SunGema/Bras_Manipulateur_V2.0/Version2.1/Assemblage_HANDrew.SLDASM

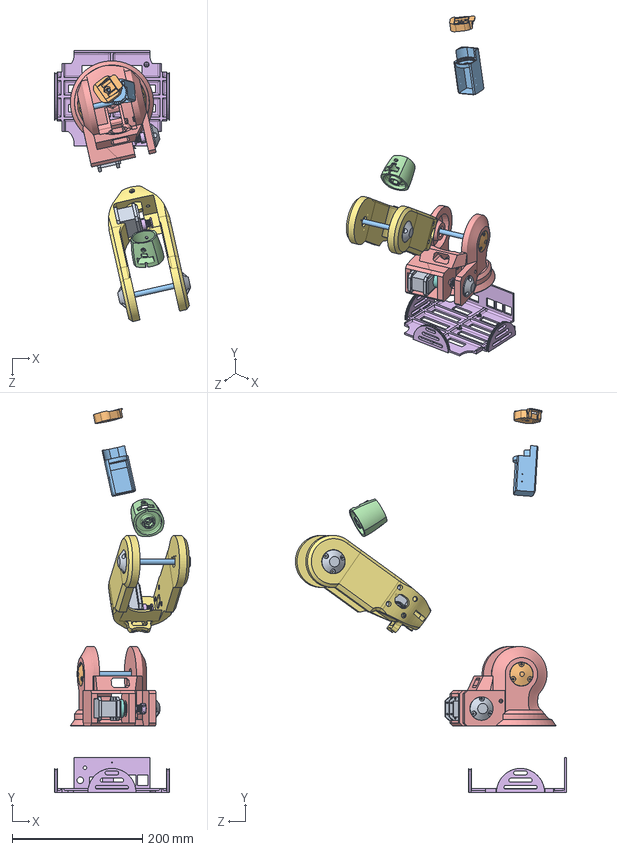
[picture p16: CAD file, 2024-02-01]
Version2.1/Assemblage_HANDrew.SLDASM
209.5 x 589.8 x 416.6 mm
support_bas
my_shoulder
my_bottom_arm
berceau_moteur
my_hand
Dynamixe_motor x 2
Support roue synchrone 2
Arm_top_V3
Roue syncrhone 2GT 20 dents x 2
bearing_e_8_01 x 7
bearing_e_8_02 x 7
Tige8x95 x 2
my_cache_shoulder x 2
my_cache_elbow x 3
