SunGema/Bras_Manipulateur_V2.0/Version 2.2 Final/Nouvelle pièce/Assemblage_Notice.SLDASM

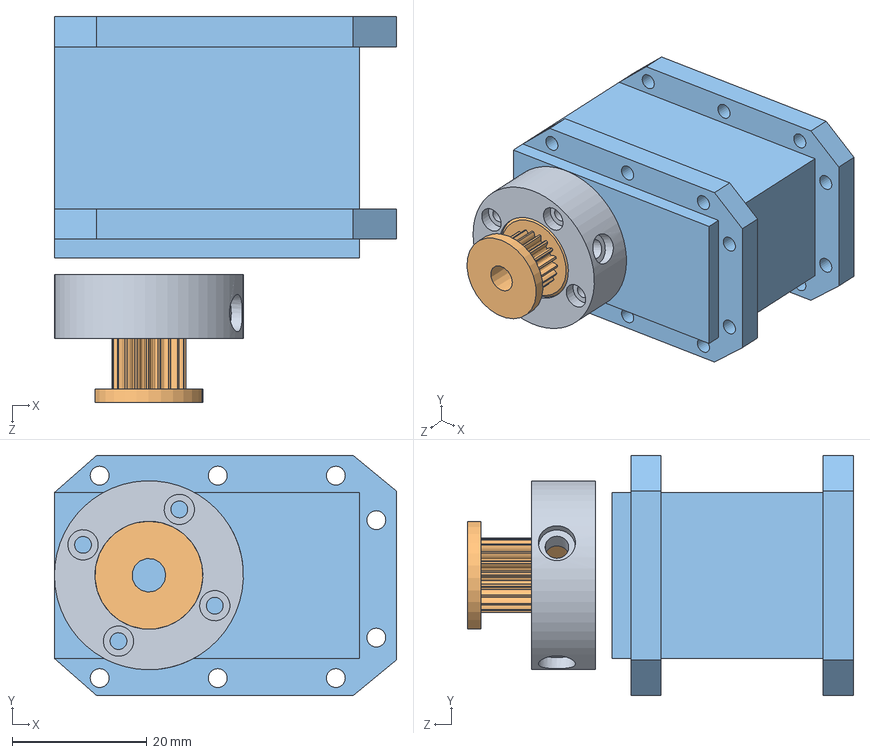
[picture p18: CAD file, 2024-02-01]
Version 2.2 Final/Nouvelle pièce/Assemblage_Notice.SLDASM
50.7 x 35.6 x 57.2 mm
Dynamixe_motor
Roue syncrhone 2GT 20 dents
Support roue synchrone 2
