SunGema/Bras_Manipulateur_V2.0/Version 2.2 Final/Nouvelle pièce/Assem2.SLDASM

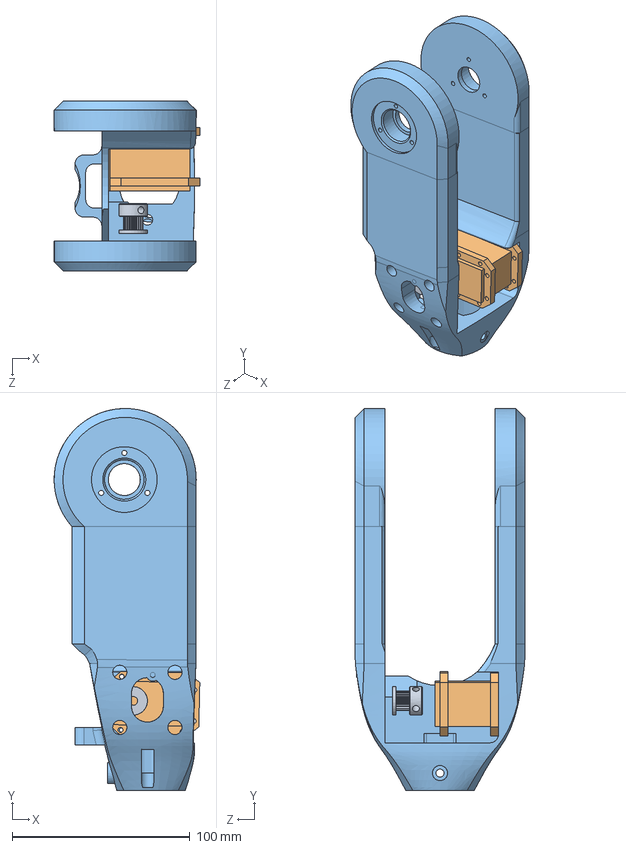
[picture p19: CAD file, 2024-02-01]
Version 2.2 Final/Nouvelle pièce/Assem2.SLDASM
82.0 x 215.0 x 95.4 mm
Arm_top_V3
Dynamixe_motor
Roue syncrhone 2GT 20 dents
