SunGema/Bras_Manipulateur_V2.0/Version 2.2 Final/Nouvelle pièce/Support roue synchrone.STL

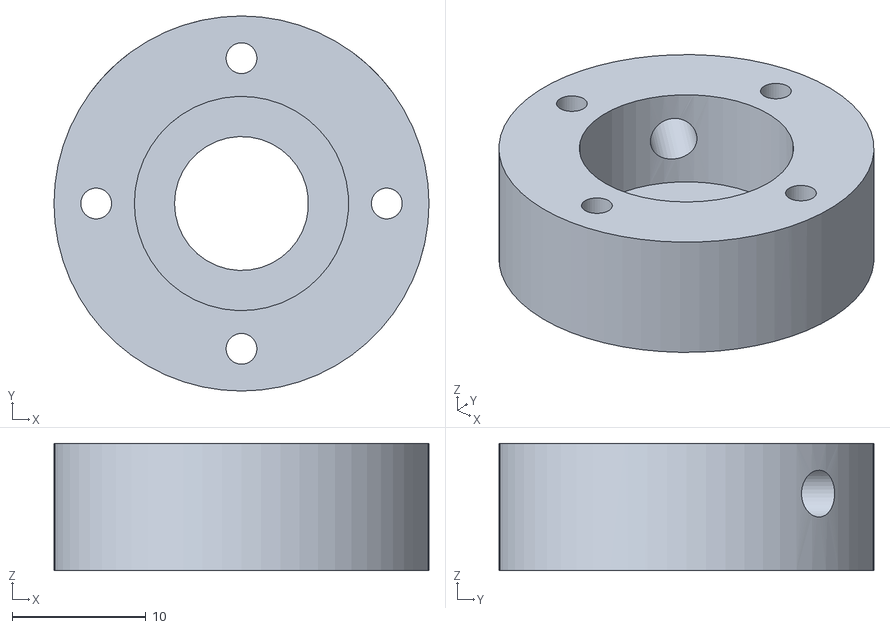
[picture p32: CAD file, 2024-02-01]
Version 2.2 Final/Nouvelle pièce/Support roue synchrone.STL
28.0 x 28.0 x 9.50
