SunGema/Bras_Manipulateur_V2.0/Version 2.2 Final/Tige/Tige8x95.SLDPRT

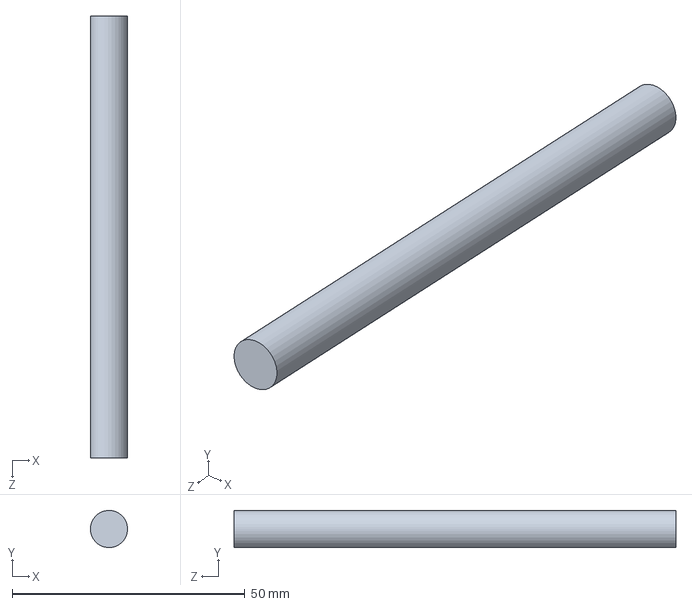
[picture p33: CAD file, 2023-12-30]
Version 2.2 Final/Tige/Tige8x95.SLDPRT
8.00 x 7.99 x 95.0 mm
