SunGema/Bras_Manipulateur_V2.0/Version2.1/143539572-7-bearing_e_8/bearing_e_8_02.SLDPRT

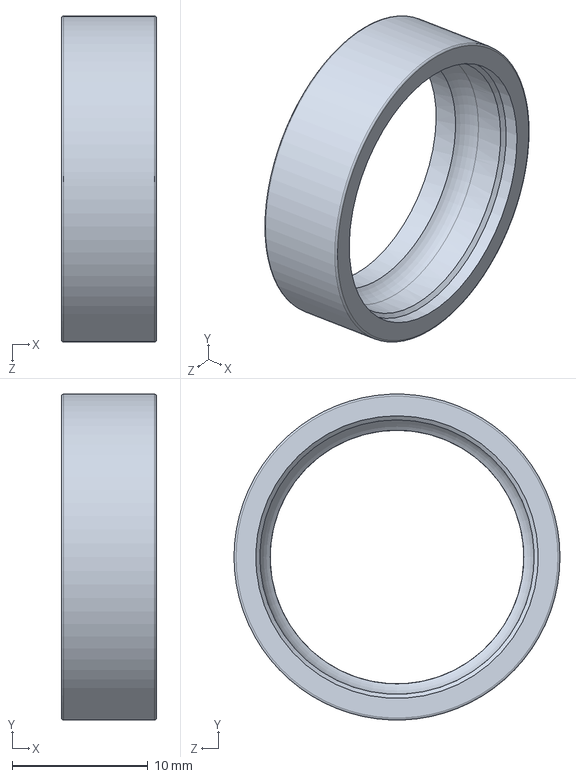
[picture p34: CAD file, 2023-12-30]
Version2.1/143539572-7-bearing_e_8/bearing_e_8_02.SLDPRT
7.00 x 24.0 x 24.0 mm
