SunGema/Bras_Manipulateur_V2.0/Version2.1/Courroie_Transmission_Base/Arm_top_V3.SLDPRT

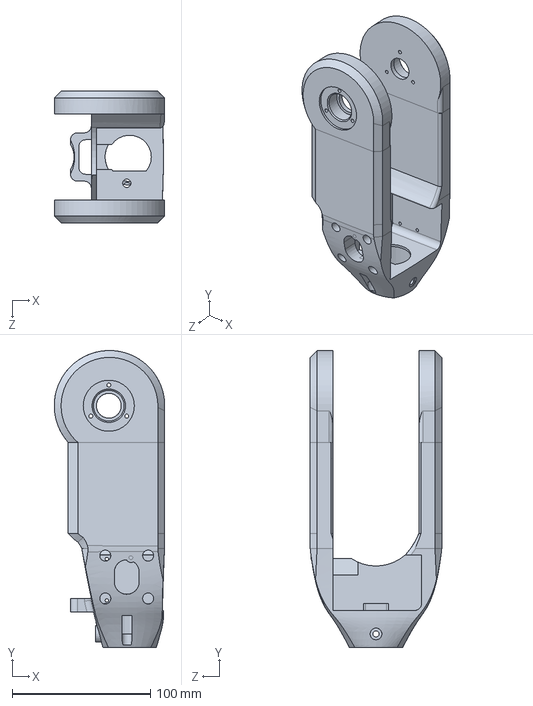
[picture p35: CAD file, 2023-11-22]
Version2.1/Courroie_Transmission_Base/Arm_top_V3.SLDPRT
80.0 x 215.0 x 95.4 mm
