SunGema/Bras_Manipulateur_V2.0/Version2.1/New_base/support_moteur_base.SLDPRT

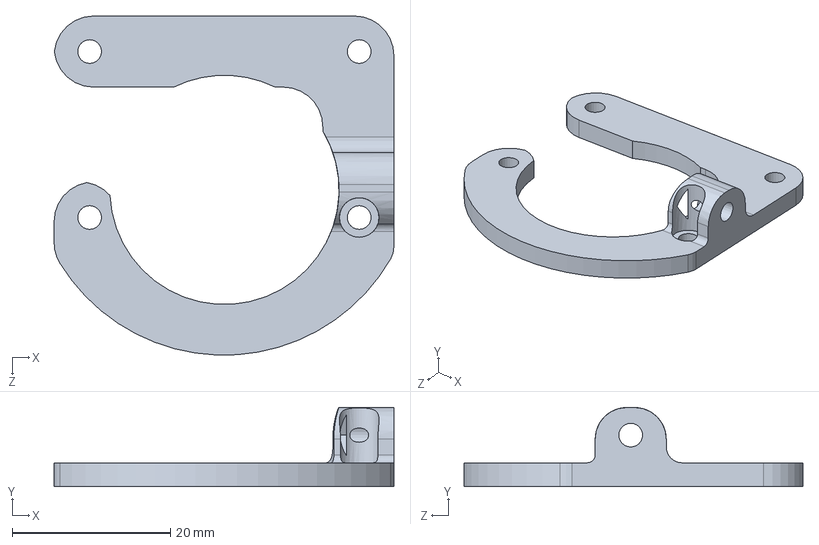
[picture p36: CAD file, 2023-12-30]
Version2.1/New_base/support_moteur_base.SLDPRT
43.0 x 10.0 x 42.9 mm
