SunGema/Bras_Manipulateur_V2.0/Version2.1/New_elbow/My_arm_top/my_arm_top_down.SLDPRT

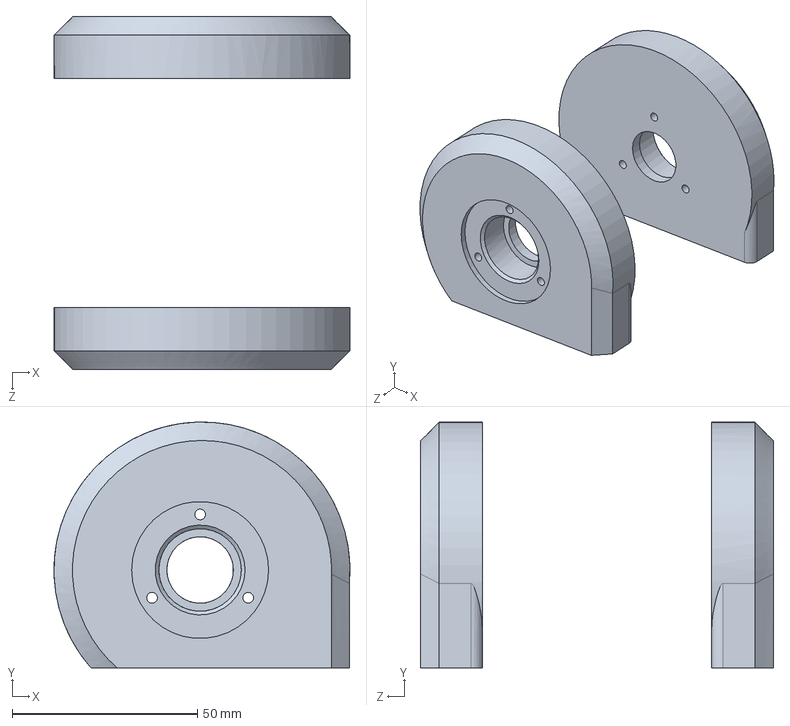
[picture p37: CAD file, 2023-12-30]
Version2.1/New_elbow/My_arm_top/my_arm_top_down.SLDPRT
80.0 x 66.5 x 95.4 mm
