SunGema/Bras_Manipulateur_V2.0/Version2.1/New_elbow/Train_epicycloidal/engrenage_satellite.SLDPRT

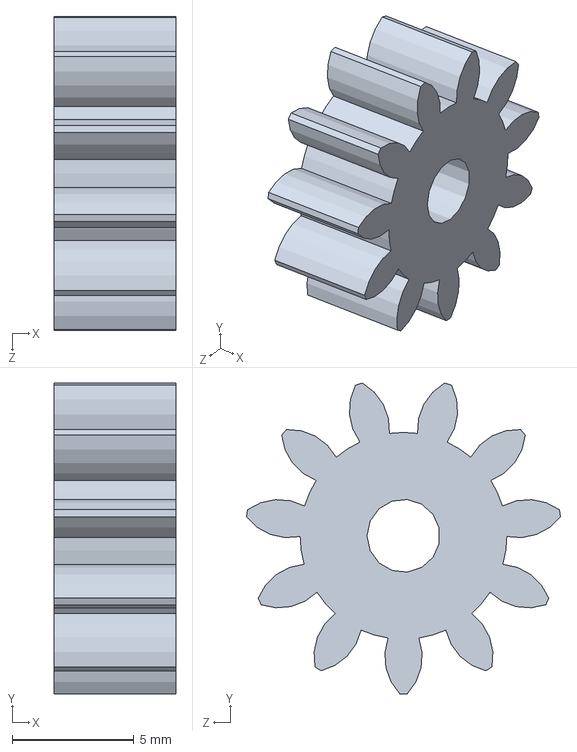
[picture p38: CAD file, 2023-12-30]
Version2.1/New_elbow/Train_epicycloidal/engrenage_satellite.SLDPRT
5.00 x 12.8 x 12.9 mm
