SunGema/Bras_Manipulateur_V2.0/Version2.1/New_shoulder/my_cache_shoulder.SLDPRT

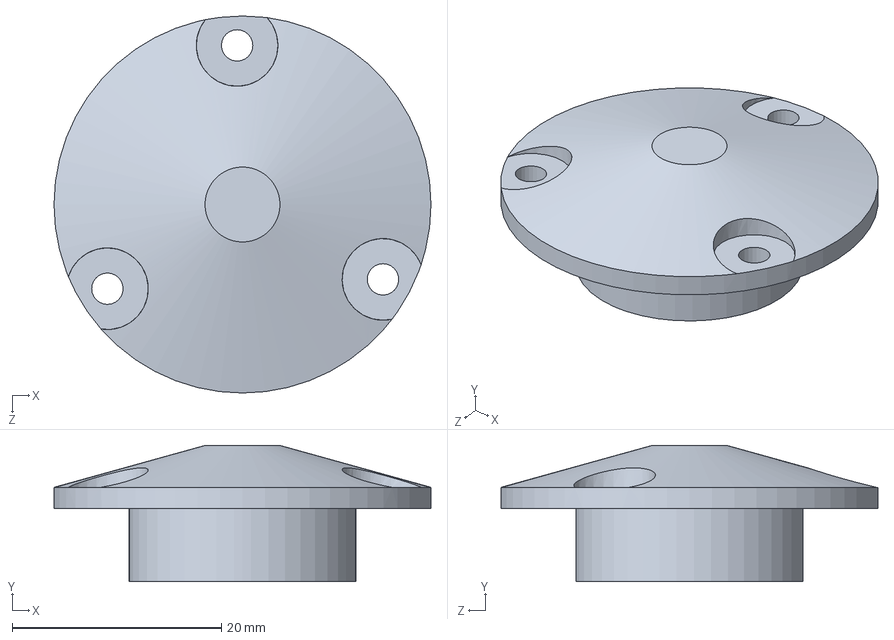
[picture p39: CAD file, 2024-02-01]
Version2.1/New_shoulder/my_cache_shoulder.SLDPRT
36.0 x 13.0 x 36.0 mm
