SunGema/Bras_Manipulateur_V2.0/Version2.1/New_wirst/STL/my_fore_arm_top.STL

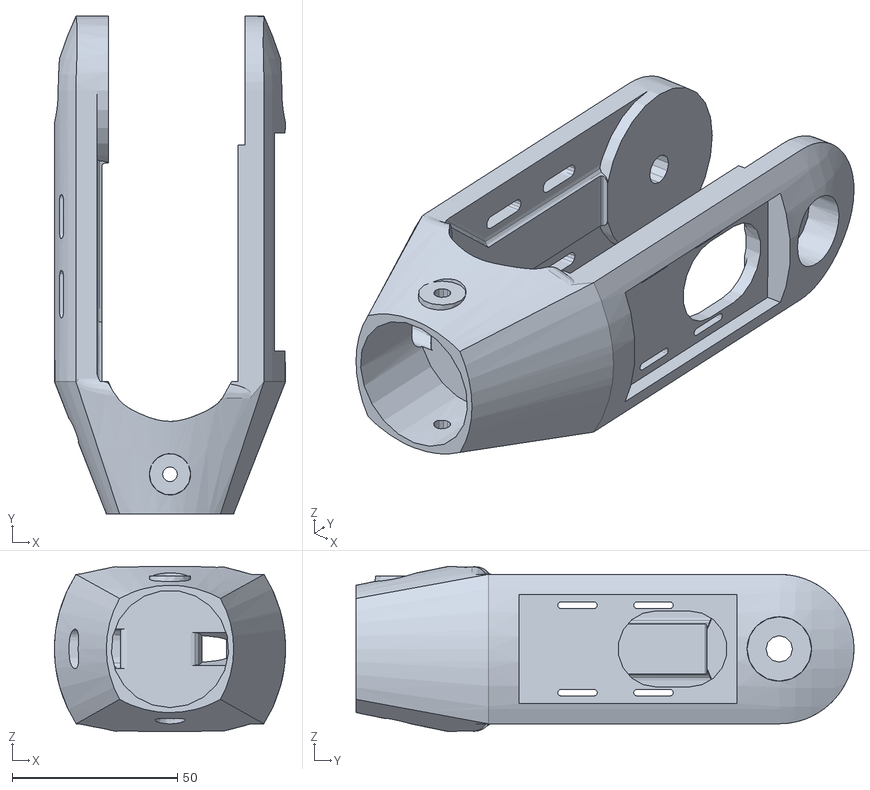
[picture p40: CAD file, 2023-12-30]
Version2.1/New_wirst/STL/my_fore_arm_top.STL
69.9 x 150.6 x 50.0
