SunGema/Bras_Manipulateur_V2.0/Version 2.2 Final/Dynamixe_motor.SLDPRT

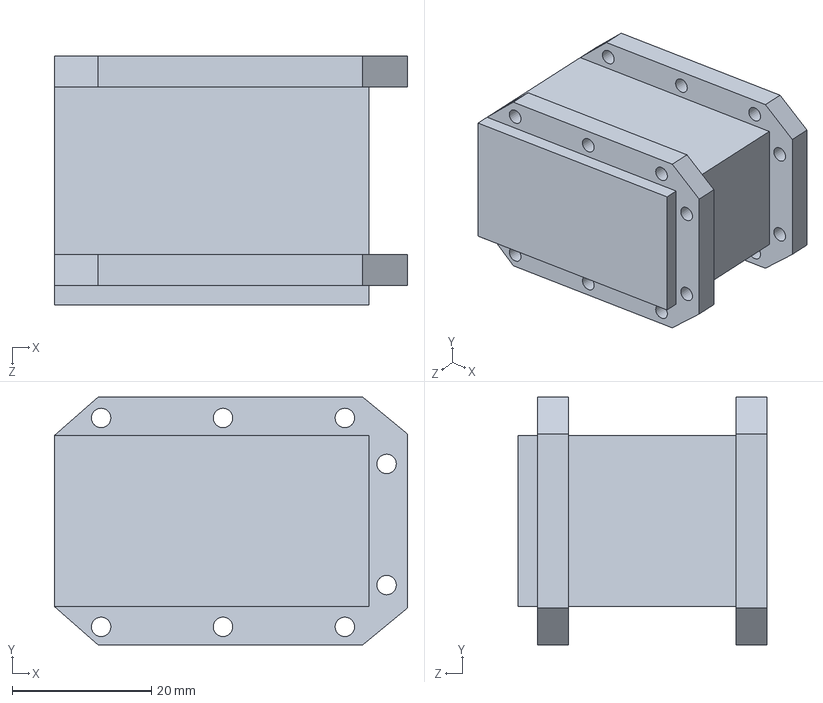
[picture p41: CAD file, 2023-12-30]
Version 2.2 Final/Dynamixe_motor.SLDPRT
50.7 x 35.6 x 35.8 mm
