SunGema/Bras_Manipulateur_V2.0/Version 2.2 Final/New_base/fixation_g.SLDPRT

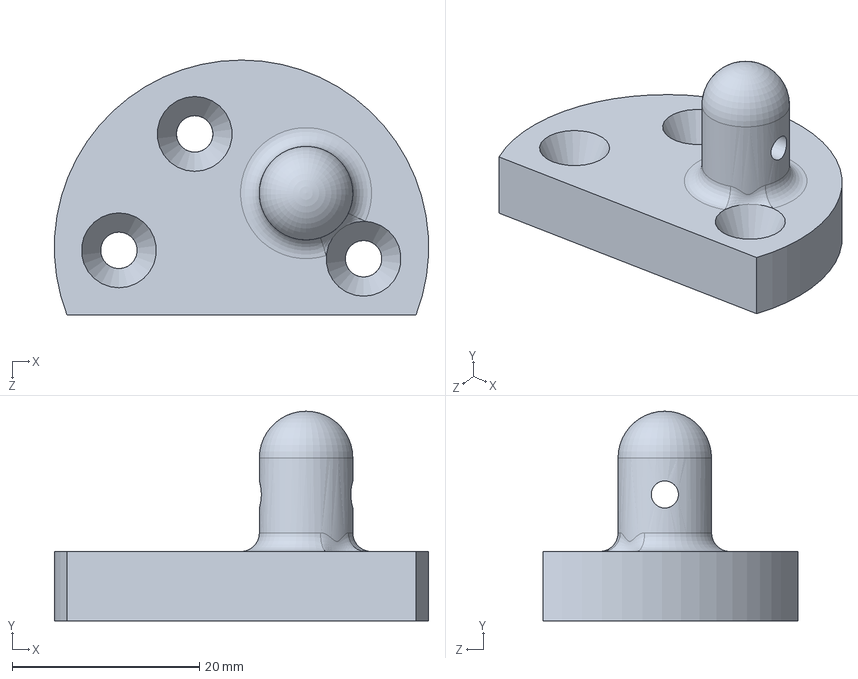
[picture p42: CAD file, 2023-12-30]
Version 2.2 Final/New_base/fixation_g.SLDPRT
40.0 x 22.4 x 27.2 mm
