SunGema/Bras_Manipulateur_V2.0/Version 2.2 Final/New_elbow/My_arm_top/my_arm_top_final.SLDPRT

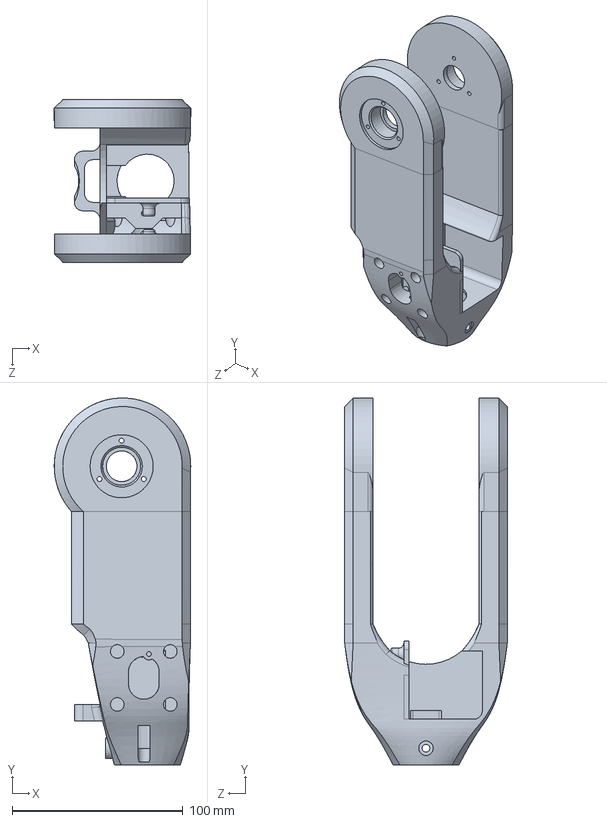
[picture p43: CAD file, 2023-12-30]
Version 2.2 Final/New_elbow/My_arm_top/my_arm_top_final.SLDPRT
80.0 x 215.0 x 95.4 mm
