SunGema/Bras_Manipulateur_V2.0/Version 2.2 Final/New_elbow/my_bottom_arm.SLDPRT

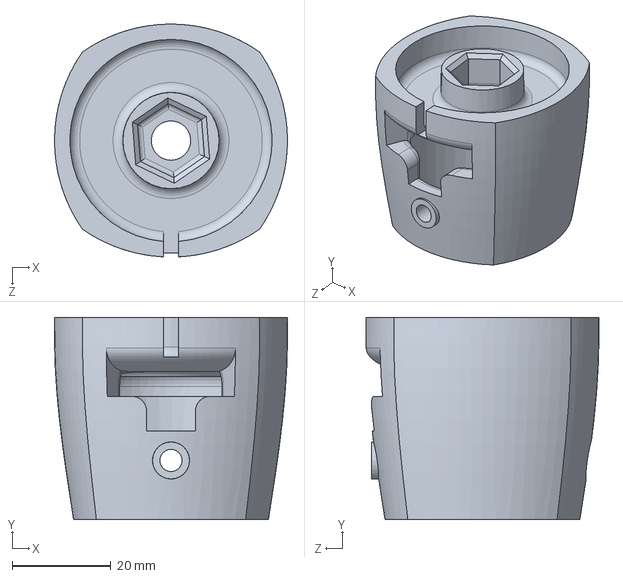
[picture p44: CAD file, 2023-12-30]
Version 2.2 Final/New_elbow/my_bottom_arm.SLDPRT
47.2 x 41.0 x 47.2 mm
