SunGema/Bras_Manipulateur_V2.0/Version 2.2 Final/New_elbow/Train_epicycloidal/bloc.SLDPRT

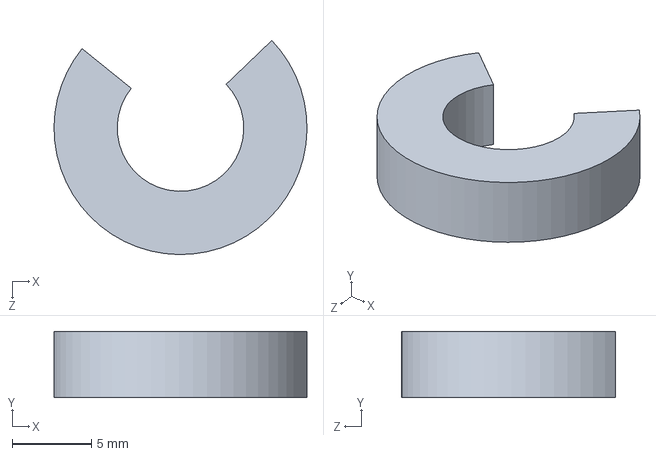
[picture p45: CAD file, 2023-12-30]
Version 2.2 Final/New_elbow/Train_epicycloidal/bloc.SLDPRT
16.0 x 4.20 x 13.5 mm
