SunGema/Bras_Manipulateur_V2.0/Version 2.2 Final/New_wirst/engrenage_moteur_wirst.SLDPRT

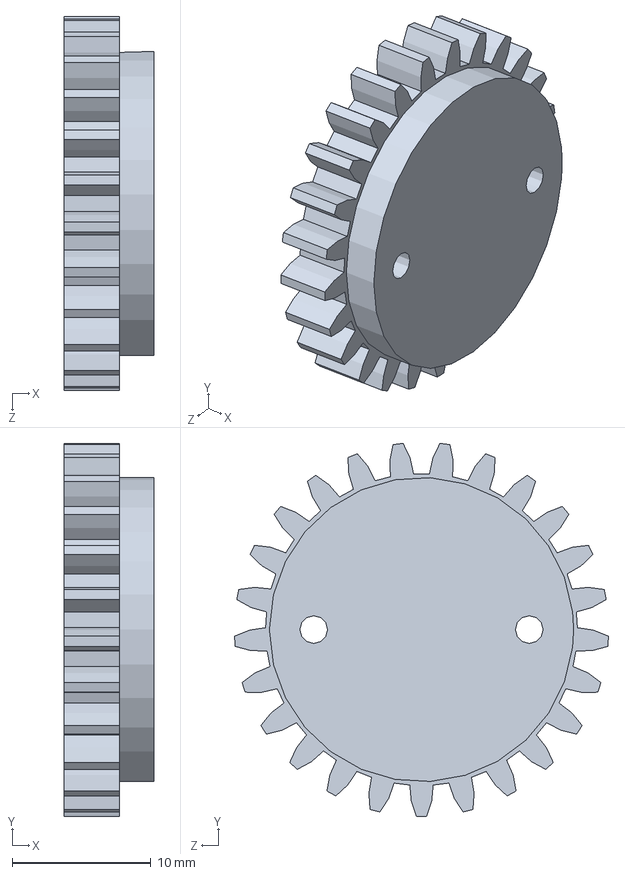
[picture p46: CAD file, 2023-12-30]
Version 2.2 Final/New_wirst/engrenage_moteur_wirst.SLDPRT
6.50 x 26.9 x 27.0 mm
