SunGema/Bras_Manipulateur_V2.0/Version 2.2 Final/New_wirst/Train_epicycloidal/satellite_wirst.SLDPRT

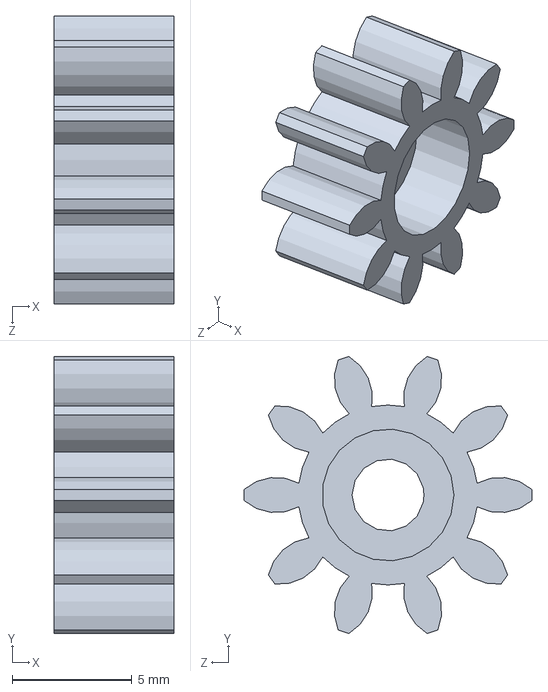
[picture p47: CAD file, 2023-12-30]
Version 2.2 Final/New_wirst/Train_epicycloidal/satellite_wirst.SLDPRT
5.00 x 11.5 x 12.0 mm
