SunGema/Bras_Manipulateur_V2.0/Version 2.2 Final/Tige/Tige8x25.SLDPRT

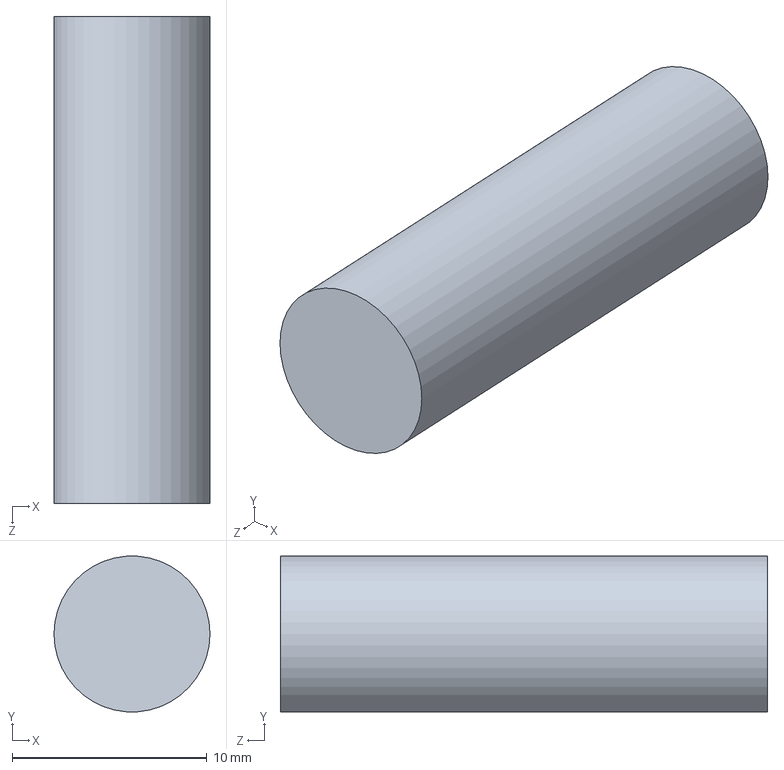
[picture p48: CAD file, 2023-12-30]
Version 2.2 Final/Tige/Tige8x25.SLDPRT
8.00 x 7.98 x 25.0 mm
