SunGema/Bras_Manipulateur_V2.0/Version2.1/New_elbow/couvercle.SLDPRT

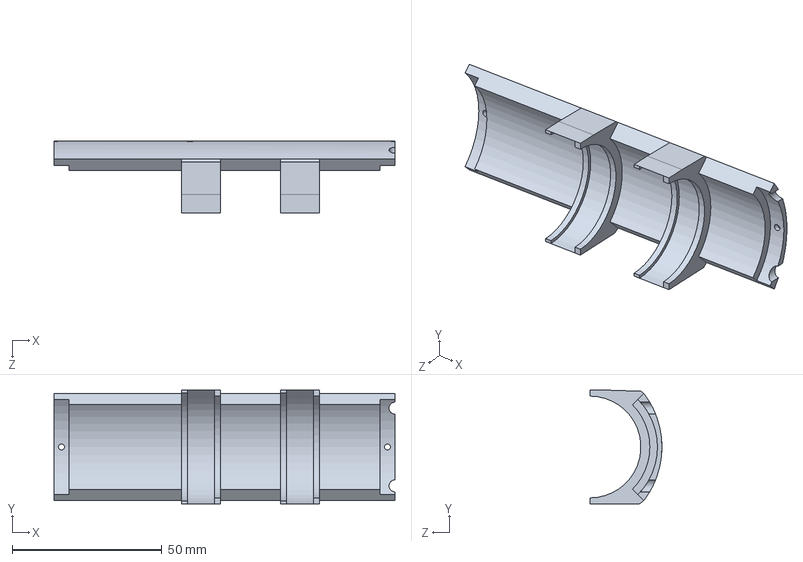
[picture p49: CAD file, 2023-12-30]
Version2.1/New_elbow/couvercle.SLDPRT
114.0 x 38.0 x 24.0 mm
