SunGema/Bras_Manipulateur_V2.0/Version2.1/New_shoulder/my_shoulder.SLDPRT

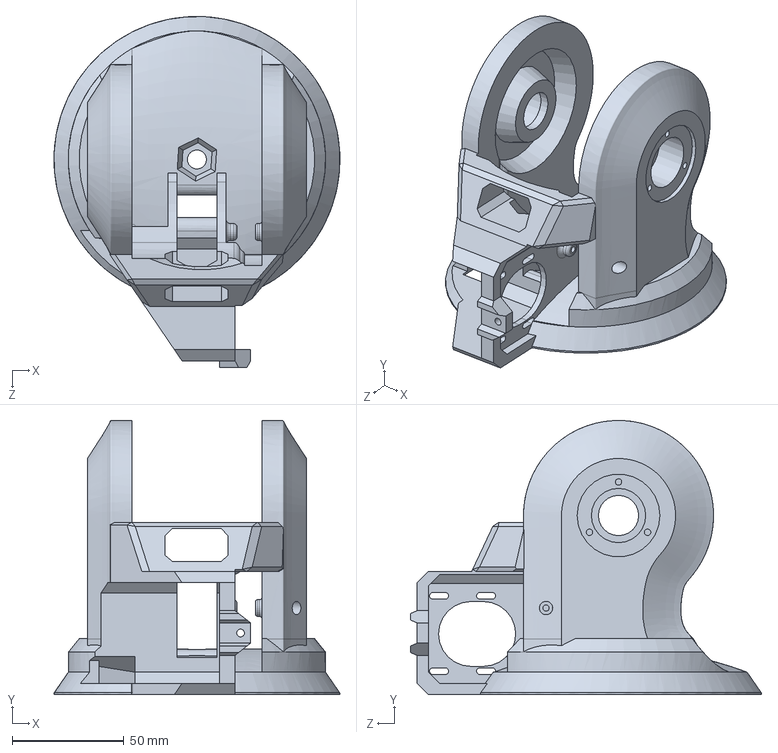
[picture p50: CAD file, 2024-02-01]
Version2.1/New_shoulder/my_shoulder.SLDPRT
127.8 x 122.5 x 156.9 mm
