SunGema/Bras_Manipulateur_V2.0/Version 2.2 Final/New_base/my_base_bearing_support.SLDPRT

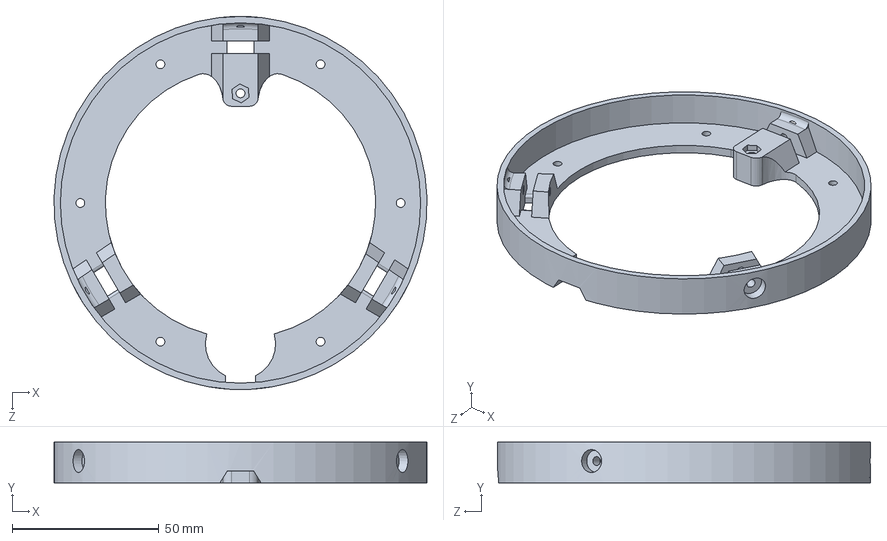
[picture p51: CAD file, 2023-12-30]
Version 2.2 Final/New_base/my_base_bearing_support.SLDPRT
126.9 x 13.8 x 127.0 mm
