SunGema/Bras_Manipulateur_V2.0/Version 2.2 Final/New_elbow/engrenage_moteur_elbow_part2.SLDPRT

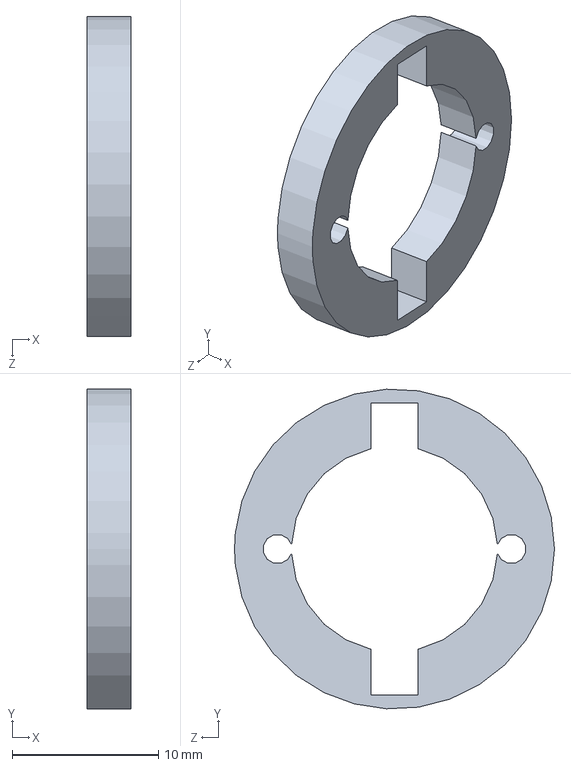
[picture p52: CAD file, 2023-12-30]
Version 2.2 Final/New_elbow/engrenage_moteur_elbow_part2.SLDPRT
3.00 x 21.9 x 21.9 mm
