SunGema/Bras_Manipulateur_V2.0/Version 2.2 Final/New_elbow/My_arm_top/my_arm_top_up.SLDPRT

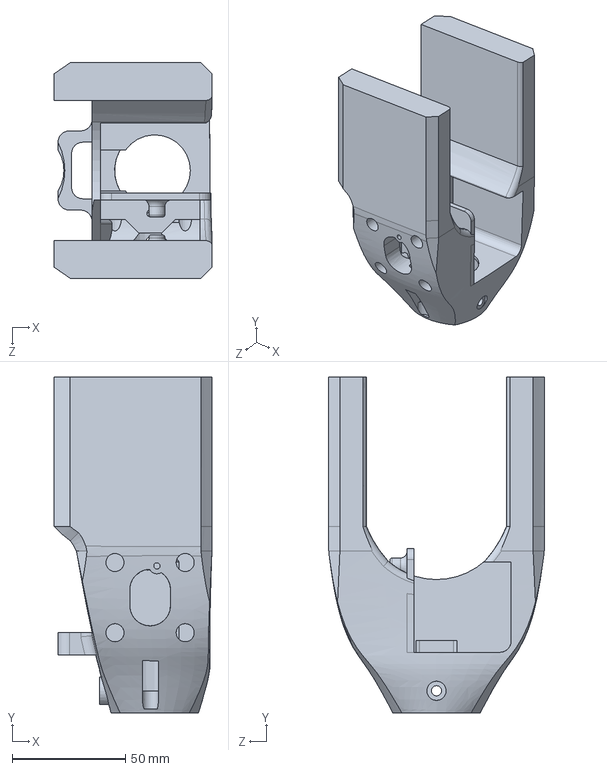
[picture p53: CAD file, 2023-12-30]
Version 2.2 Final/New_elbow/My_arm_top/my_arm_top_up.SLDPRT
69.8 x 148.5 x 95.4 mm
