SunGema/Bras_Manipulateur_V2.0/Version 2.2 Final/New_elbow/Train_epicycloidal/planetaire.SLDPRT

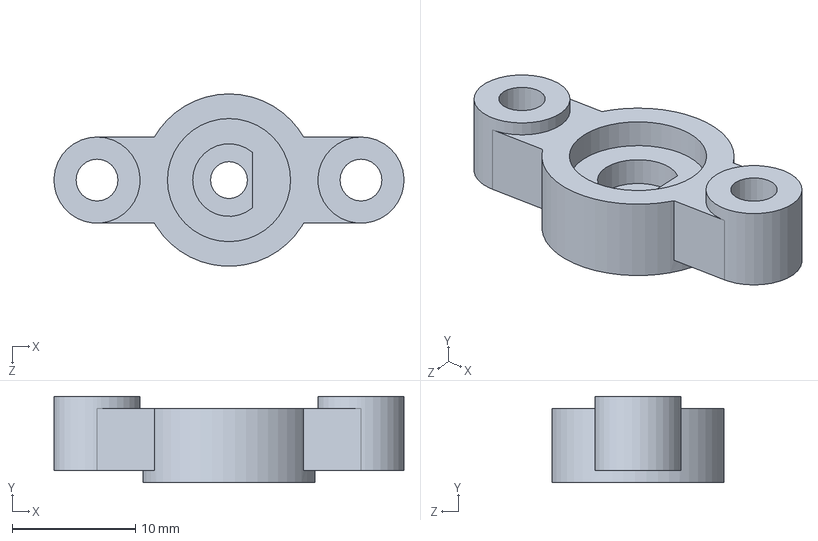
[picture p54: CAD file, 2023-12-30]
Version 2.2 Final/New_elbow/Train_epicycloidal/planetaire.SLDPRT
28.4 x 7.00 x 14.0 mm
