SunGema/Bras_Manipulateur_V2.0/Version 2.2 Final/New_shoulder/my_roundtube.SLDPRT

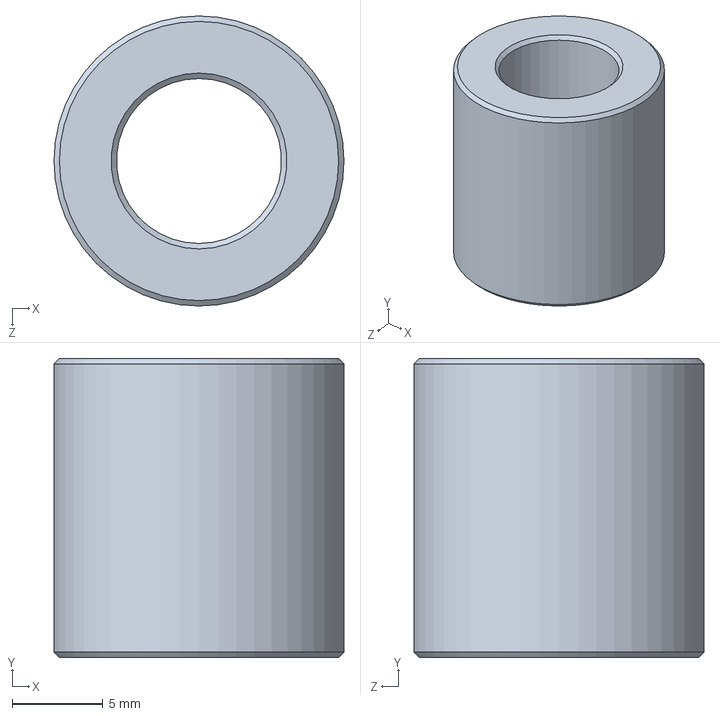
[picture p55: CAD file, 2023-12-30]
Version 2.2 Final/New_shoulder/my_roundtube.SLDPRT
16.0 x 16.5 x 16.0 mm
