SunGema/Bras_Manipulateur_V2.0/Version 2.2 Final/Tige/Tige8x45.SLDPRT

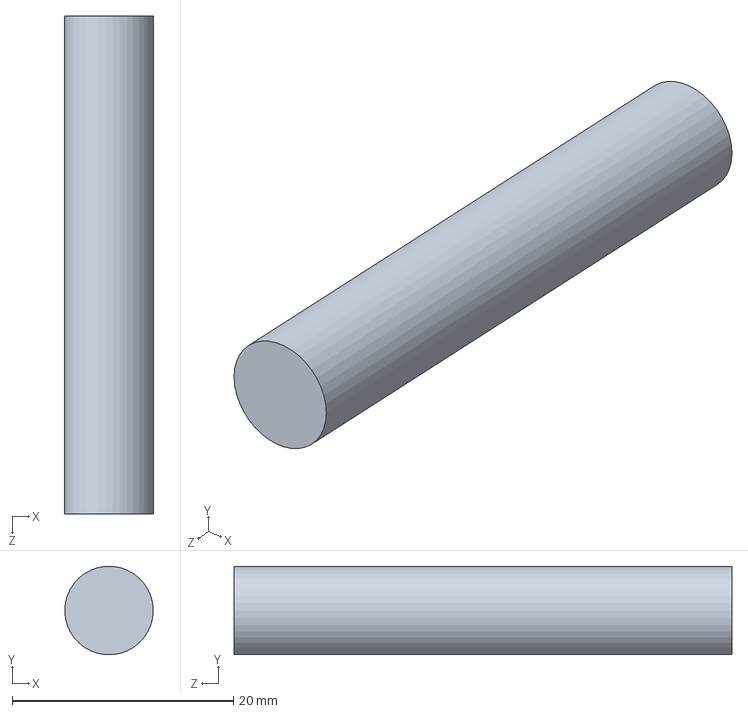
[picture p56: CAD file, 2023-12-30]
Version 2.2 Final/Tige/Tige8x45.SLDPRT
8.00 x 7.97 x 45.0 mm
