SunGema/Bras_Manipulateur_V2.0/Version 2.2 Final/tube_bottom.SLDPRT

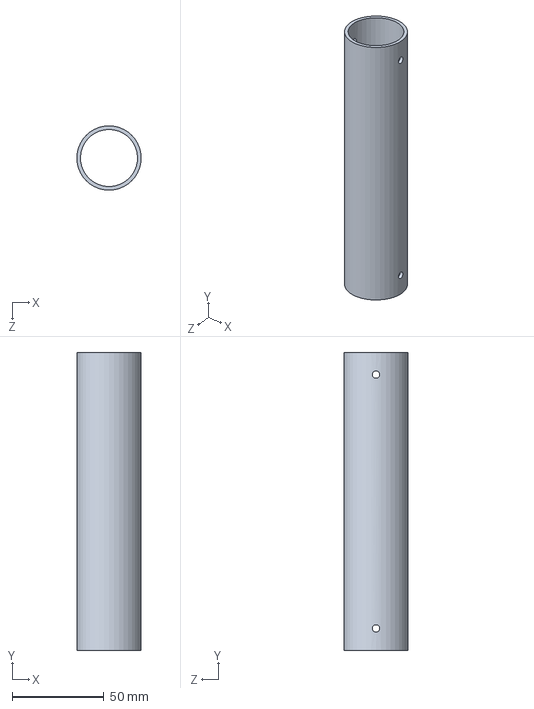
[picture p57: CAD file, 2023-12-30]
Version 2.2 Final/tube_bottom.SLDPRT
35.0 x 162.0 x 35.0 mm
