SunGema/Bras_Manipulateur_V2.0/Version2.1/143539572-7-bearing_e_8/bearing_e_8_03.SLDPRT

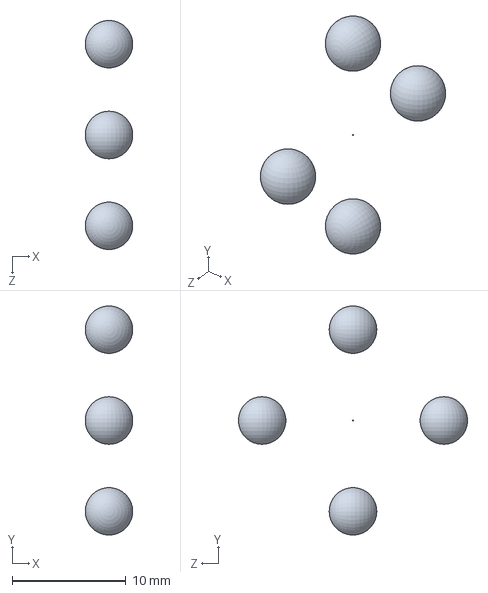
[picture p58: CAD file, 2023-12-30]
Version2.1/143539572-7-bearing_e_8/bearing_e_8_03.SLDPRT
4.18 x 20.2 x 20.2 mm
