SunGema/Bras_Manipulateur_V2.0/Version2.1/New_elbow/support_moteur.SLDPRT

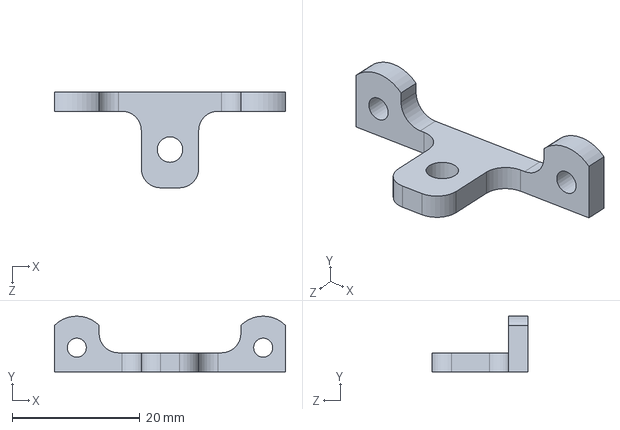
[picture p59: CAD file, 2023-12-30]
Version2.1/New_elbow/support_moteur.SLDPRT
36.2 x 8.75 x 15.0 mm
