SunGema/Bras_Manipulateur_V2.0/Version2.1/New_wirst/berceau_axe.SLDPRT

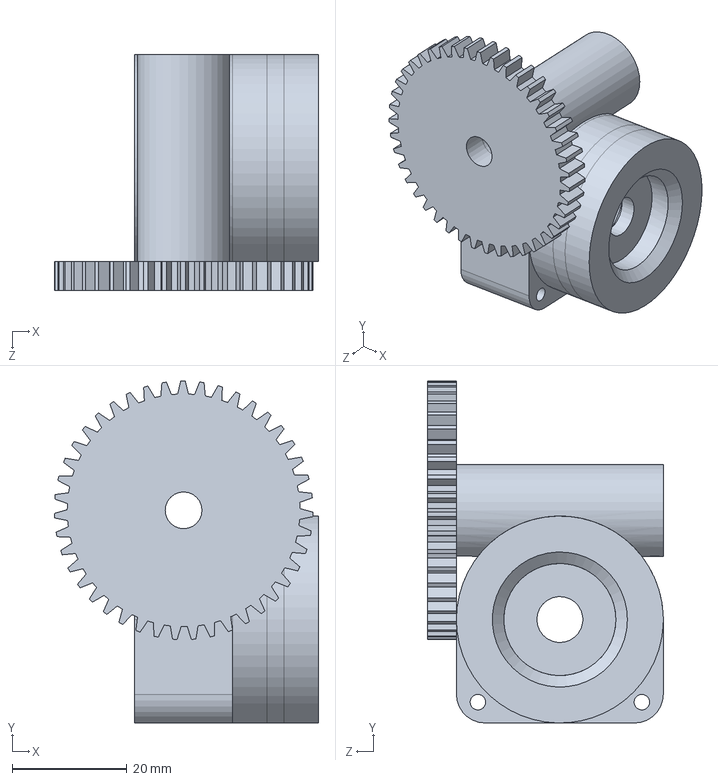
[picture p60: CAD file, 2023-12-30]
Version2.1/New_wirst/berceau_axe.SLDPRT
46.0 x 59.5 x 41.0 mm
