SunGema/Bras_Manipulateur_V2.0/Version2.1/New_wirst/Train_epicycloidal/accroche_vis_berceau.SLDPRT

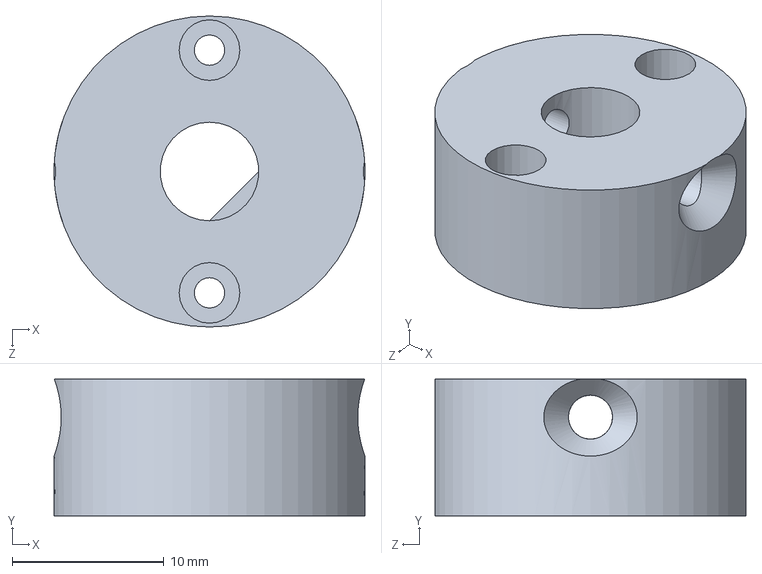
[picture p61: CAD file, 2023-12-30]
Version2.1/New_wirst/Train_epicycloidal/accroche_vis_berceau.SLDPRT
20.5 x 9.00 x 20.5 mm
