SunGema/Bras_Manipulateur_V2.0/Version2.1/tube_top.SLDPRT

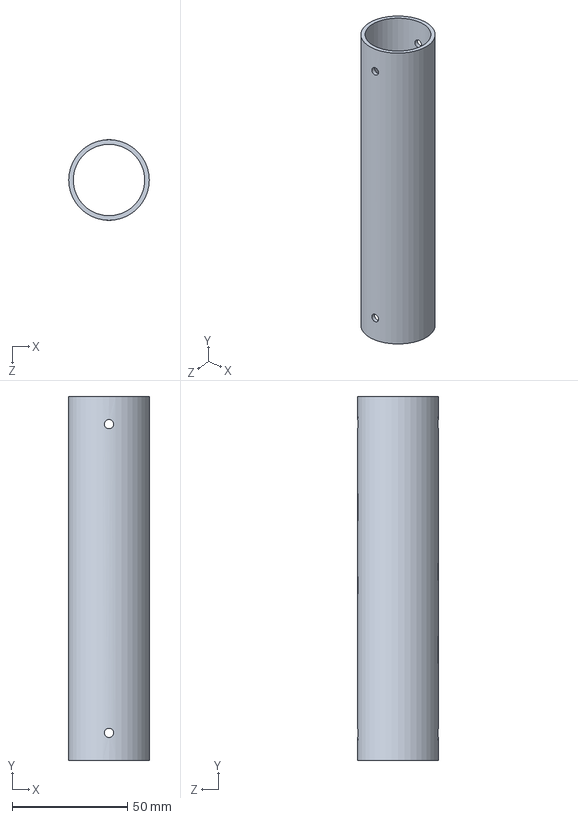
[picture p62: CAD file, 2023-12-30]
Version2.1/tube_top.SLDPRT
35.0 x 158.0 x 35.0 mm
