SunGema/Bras_Manipulateur_V2.0/Version 2.2 Final/New_elbow/Train_epicycloidal/planetaire_fin.SLDPRT

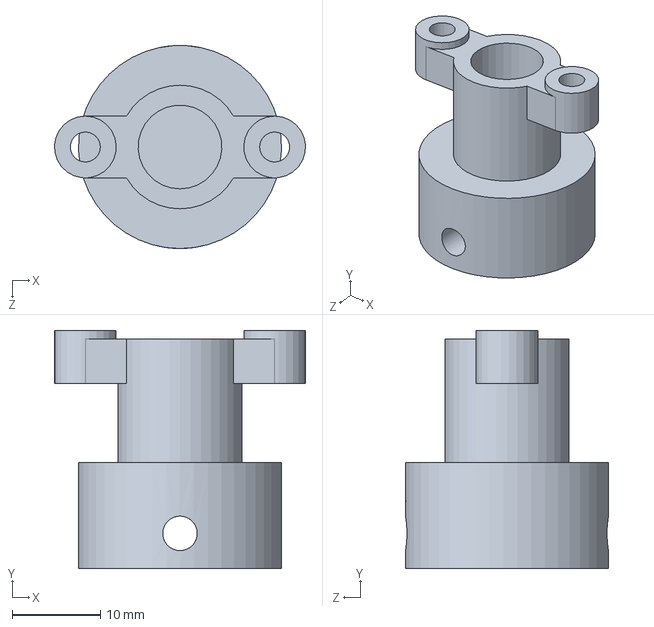
[picture p63: CAD file, 2023-12-30]
Version 2.2 Final/New_elbow/Train_epicycloidal/planetaire_fin.SLDPRT
28.4 x 27.0 x 23.0 mm
