SunGema/Bras_Manipulateur_V2.0/Version 2.2 Final/New_shoulder/engrenage_moteur_shoulder_part2.SLDPRT

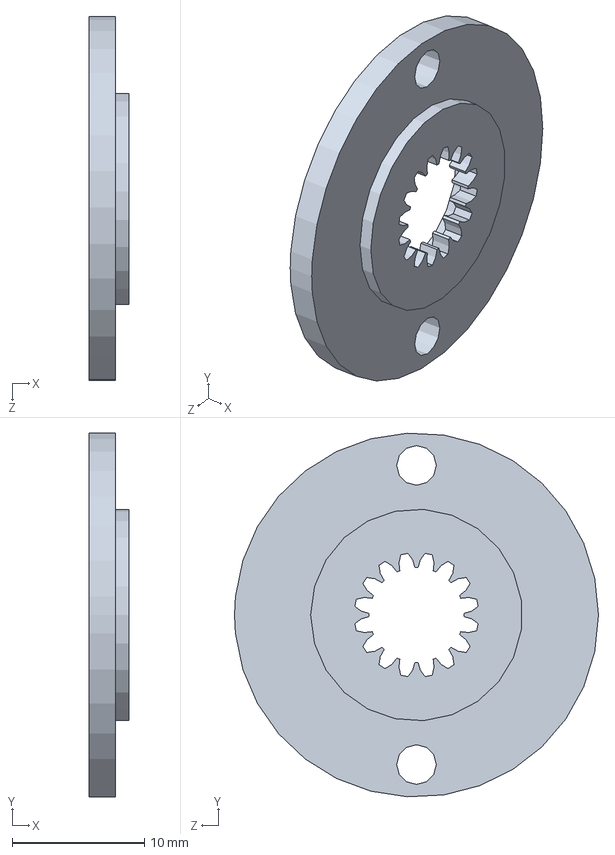
[picture p64: CAD file, 2023-12-30]
Version 2.2 Final/New_shoulder/engrenage_moteur_shoulder_part2.SLDPRT
3.00 x 27.5 x 27.5 mm
