SunGema/Bras_Manipulateur_V2.0/Version 2.2 Final/Nouvelle pièce/Support roue synchrone 2.SLDPRT

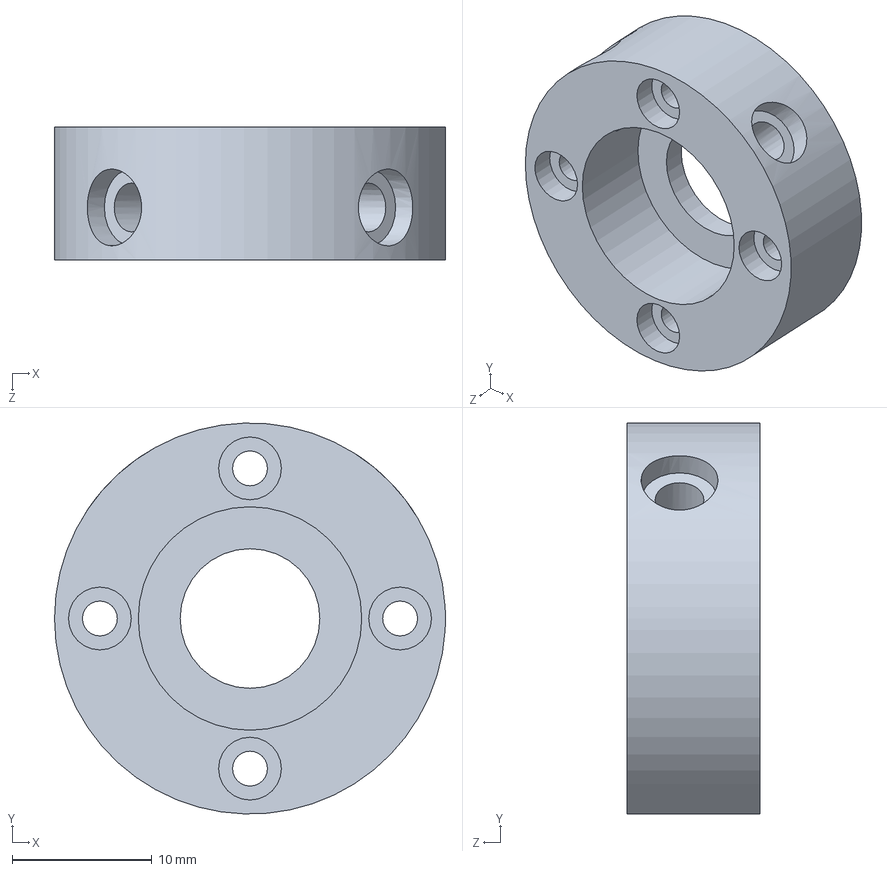
[picture p65: CAD file, 2024-02-01]
Version 2.2 Final/Nouvelle pièce/Support roue synchrone 2.SLDPRT
28.0 x 28.0 x 9.50 mm
