SunGema/Bras_Manipulateur_V2.0/Version2.1/New_elbow/accroche_vis.SLDPRT

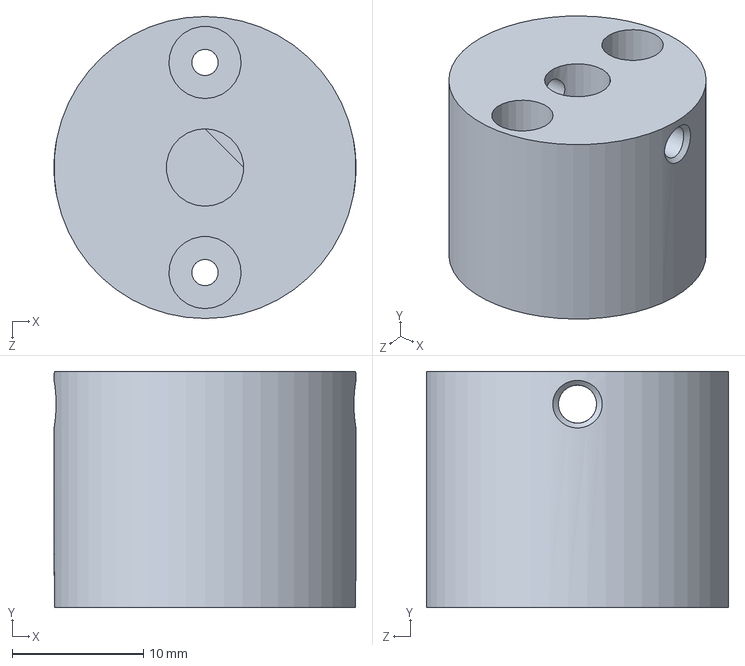
[picture p66: CAD file, 2023-12-30]
Version2.1/New_elbow/accroche_vis.SLDPRT
23.0 x 18.0 x 23.0 mm
