SunGema/Bras_Manipulateur_V2.0/Version2.1/New_shoulder/engrenage_moteur_shoulder.SLDPRT

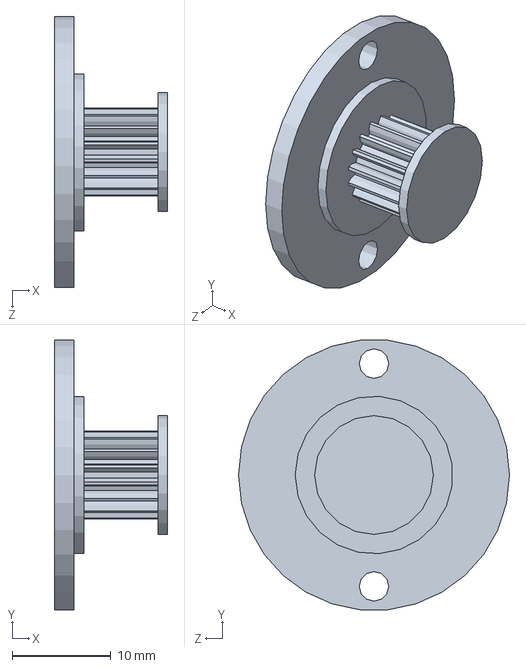
[picture p67: CAD file, 2023-12-30]
Version2.1/New_shoulder/engrenage_moteur_shoulder.SLDPRT
11.5 x 27.3 x 27.5 mm
