SunGema/Bras_Manipulateur_V2.0/Version 2.2 Final/New_base/my_base.SLDPRT

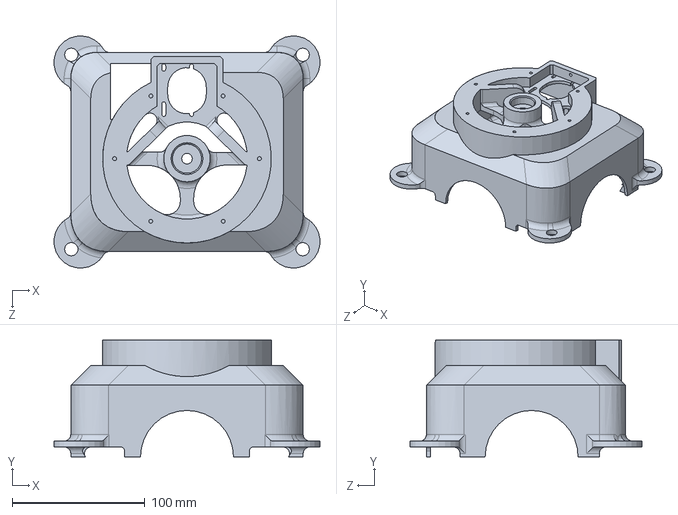
[picture p68: CAD file, 2023-12-30]
Version 2.2 Final/New_base/my_base.SLDPRT
200.3 x 88.0 x 174.8 mm
