SunGema/Bras_Manipulateur_V2.0/Version 2.2 Final/New_elbow/Train_epicycloidal/engrenage_couronne.SLDPRT

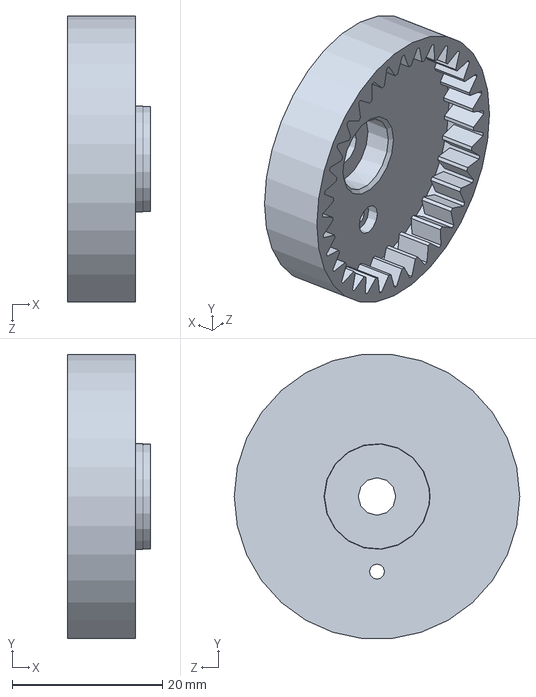
[picture p69: CAD file, 2023-12-30]
Version 2.2 Final/New_elbow/Train_epicycloidal/engrenage_couronne.SLDPRT
11.0 x 37.8 x 38.0 mm
