SunGema/Bras_Manipulateur_V2.0/Version 2.2 Final/New_shoulder/engrenage_moteur_shoulder_part1.SLDPRT

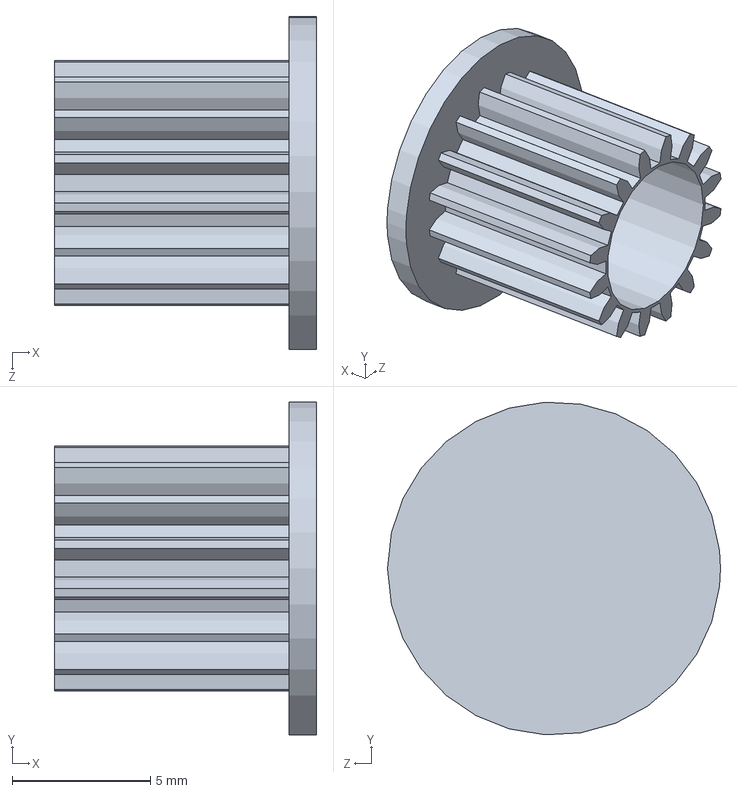
[picture p70: CAD file, 2023-12-30]
Version 2.2 Final/New_shoulder/engrenage_moteur_shoulder_part1.SLDPRT
9.50 x 12.0 x 12.1 mm
