SunGema/Bras_Manipulateur_V2.0/Version2.1/New_base/engrenage_moteur.SLDPRT

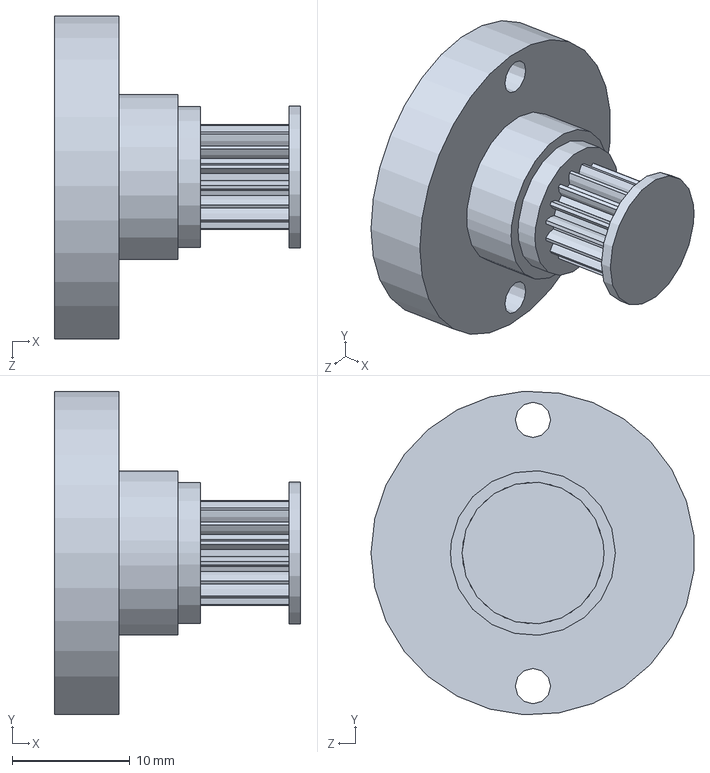
[picture p71: CAD file, 2023-12-30]
Version2.1/New_base/engrenage_moteur.SLDPRT
20.9 x 27.5 x 27.4 mm
