SunGema/Bras_Manipulateur_V2.0/Version2.1/New_elbow/blocage_couronne.SLDPRT

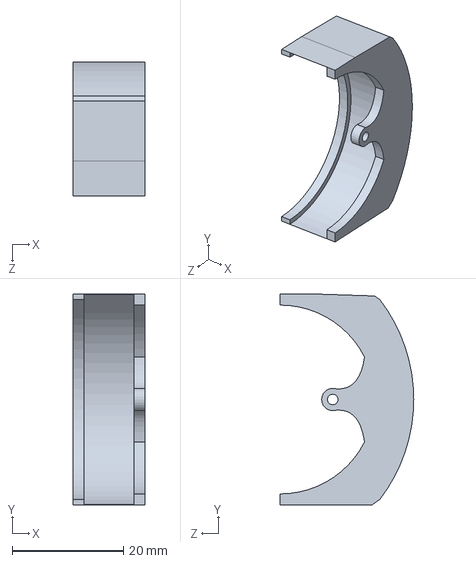
[picture p72: CAD file, 2023-12-30]
Version2.1/New_elbow/blocage_couronne.SLDPRT
13.0 x 38.0 x 24.0 mm
