SunGema/Bras_Manipulateur_V2.0/Version 2.2 Final/New_elbow/engrenage_moteur_elbow.SLDPRT

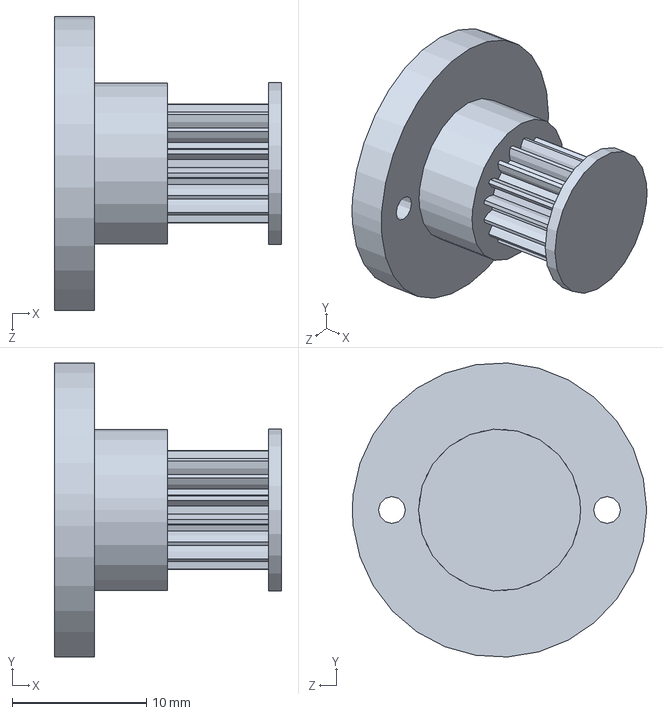
[picture p73: CAD file, 2023-12-30]
Version 2.2 Final/New_elbow/engrenage_moteur_elbow.SLDPRT
16.9 x 21.9 x 21.9 mm
