SunGema/Bras_Manipulateur_V2.0/Version2.1/New_shoulder/support_motor_shoulder.SLDPRT

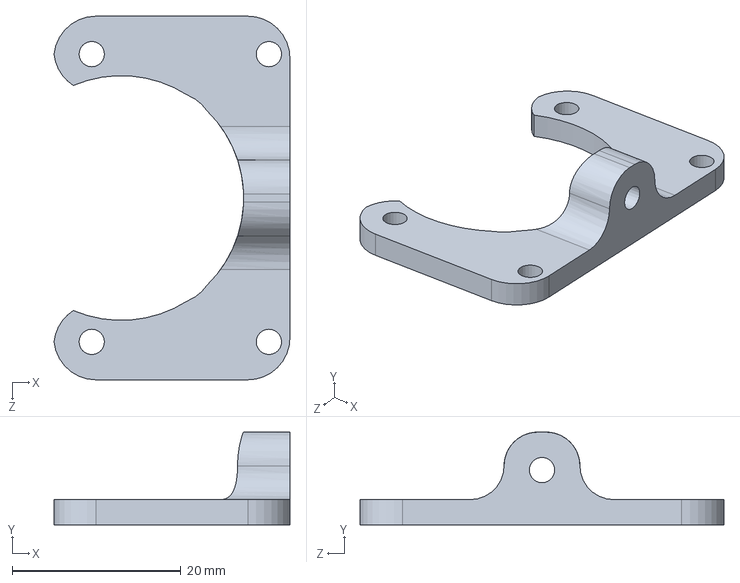
[picture p74: CAD file, 2023-12-30]
Version2.1/New_shoulder/support_motor_shoulder.SLDPRT
28.0 x 11.0 x 43.1 mm
