SunGema/Bras_Manipulateur_V2.0/Version 2.2 Final/New_elbow/my_elbow.SLDPRT

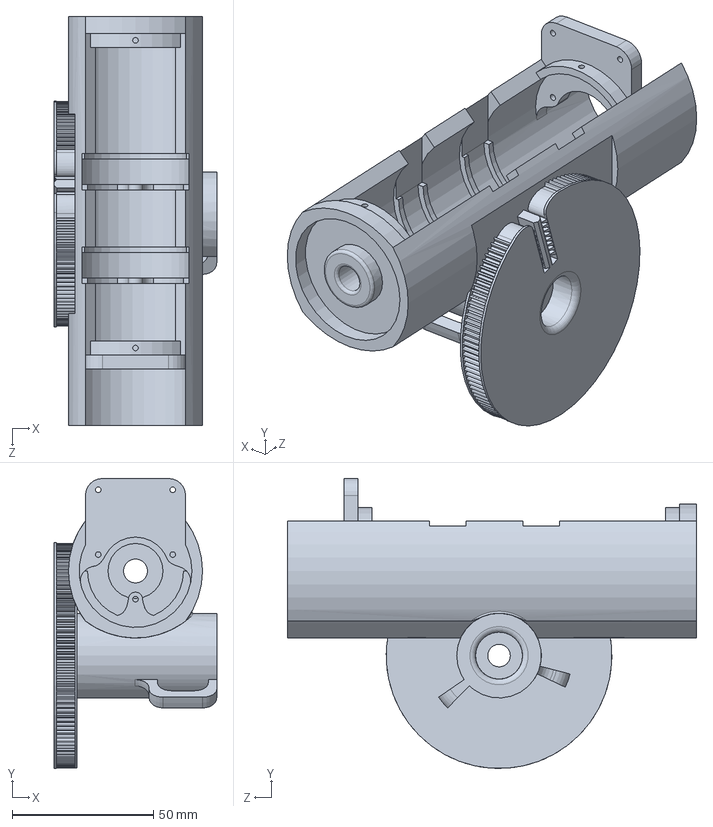
[picture p75: CAD file, 2023-12-30]
Version 2.2 Final/New_elbow/my_elbow.SLDPRT
57.6 x 102.8 x 145.0 mm
