SunGema/Bras_Manipulateur_V2.0/Version 2.2 Final/Nouvelle pièce/support moteur.SLDPRT

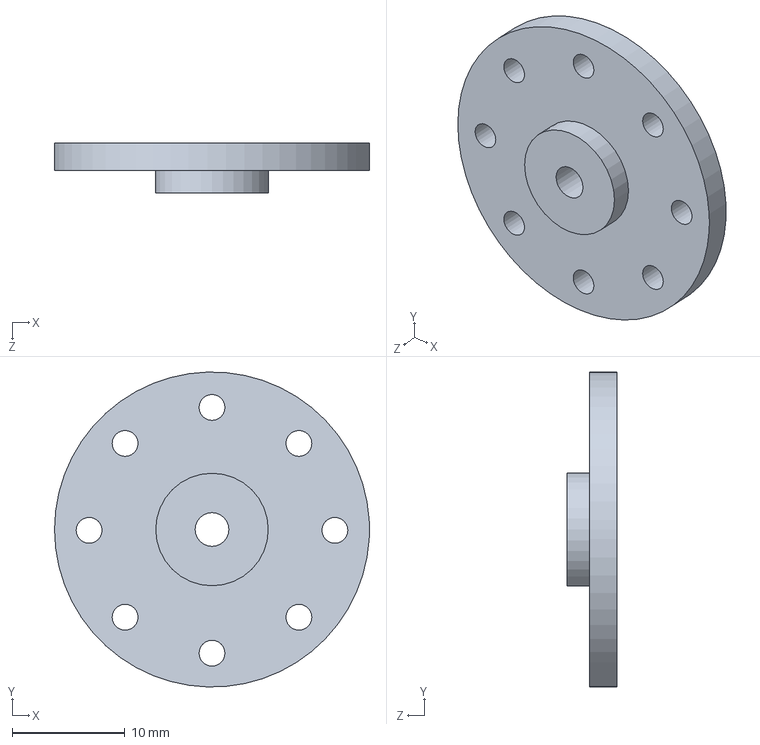
[picture p76: CAD file, 2024-02-01]
Version 2.2 Final/Nouvelle pièce/support moteur.SLDPRT
28.0 x 28.0 x 4.40 mm
