SunGema/Bras_Manipulateur_V2.0/Version2.1/New_elbow/engrenage_moteur_elbow_part1.SLDPRT

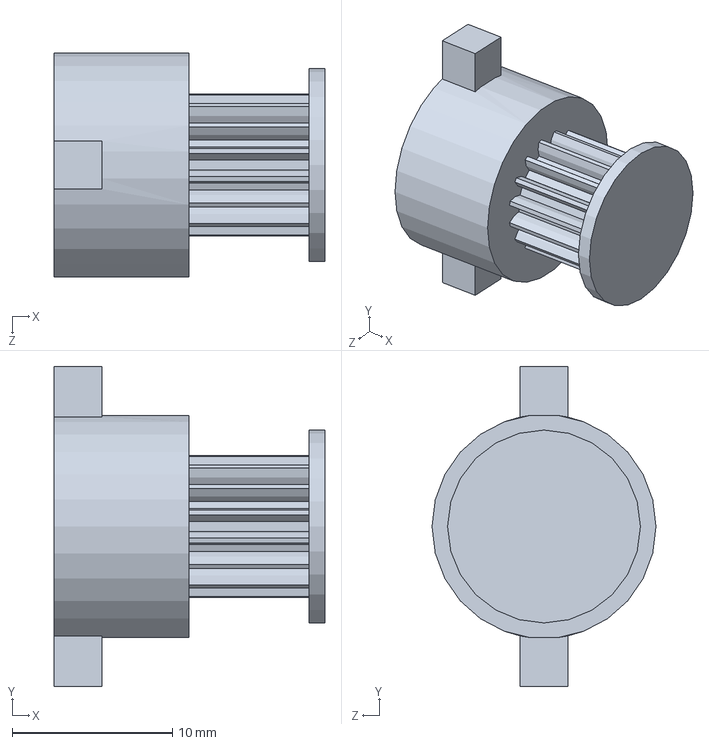
[picture p77: CAD file, 2023-12-30]
Version2.1/New_elbow/engrenage_moteur_elbow_part1.SLDPRT
16.9 x 20.0 x 14.0 mm
