SunGema/Bras_Manipulateur_V2.0/Version 2.2 Final/New_shoulder/my_arm_bottom.SLDPRT

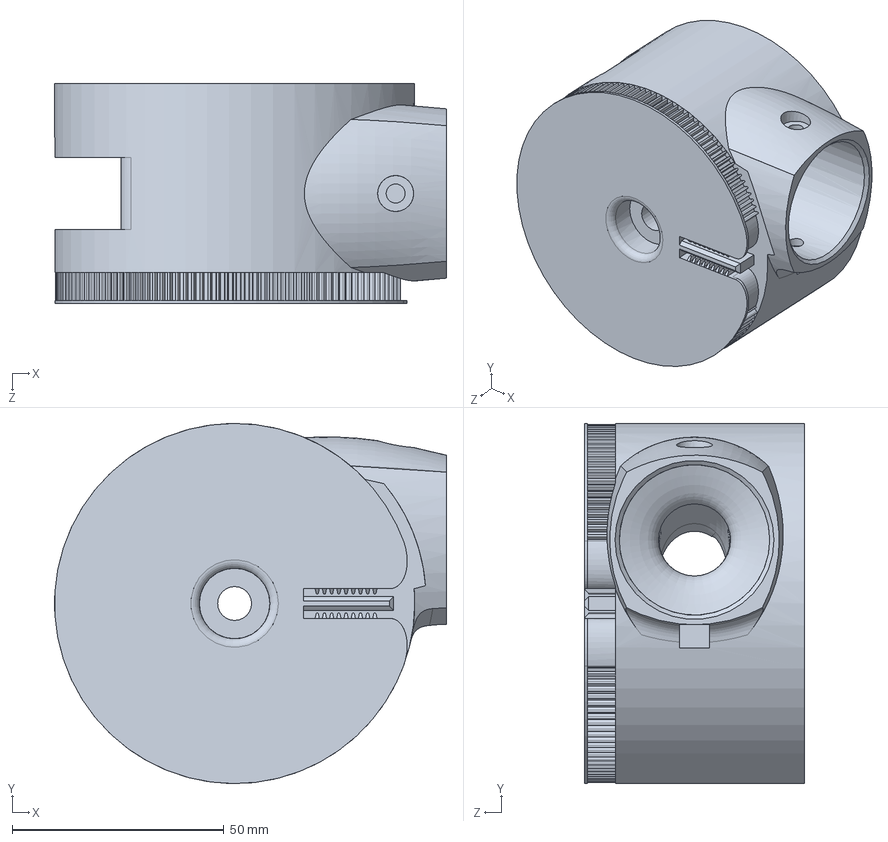
[picture p78: CAD file, 2023-12-30]
Version 2.2 Final/New_shoulder/my_arm_bottom.SLDPRT
92.5 x 85.0 x 52.0 mm
