SunGema/Bras_Manipulateur_V2.0/Version 2.2 Final/New_shoulder/my_gearing.SLDPRT

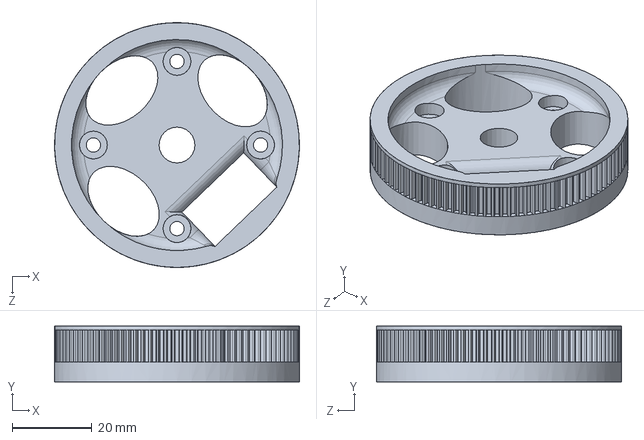
[picture p79: CAD file, 2023-12-30]
Version 2.2 Final/New_shoulder/my_gearing.SLDPRT
61.5 x 14.0 x 61.5 mm
