SunGema/Bras_Manipulateur_V2.0/Version 2.2 Final/Nouvelle pièce/Tige8x60.SLDPRT

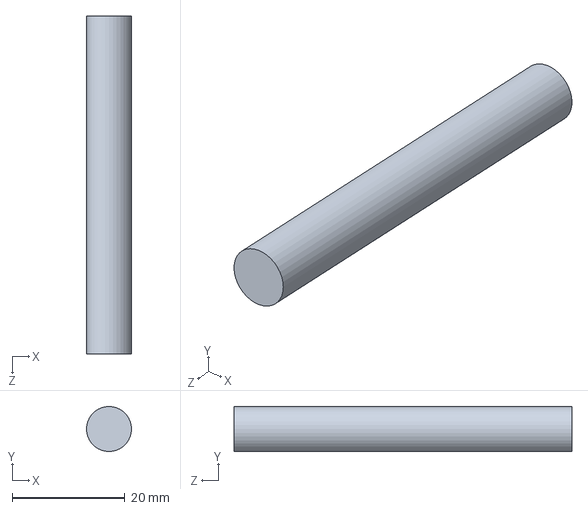
[picture p80: CAD file, 2024-02-01]
Version 2.2 Final/Nouvelle pièce/Tige8x60.SLDPRT
8.00 x 8.00 x 60.0 mm
