SunGema/Bras_Manipulateur_V2.0/Version 2.2 Final/Nouvelle pièce/tunable-gear.SLDPRT

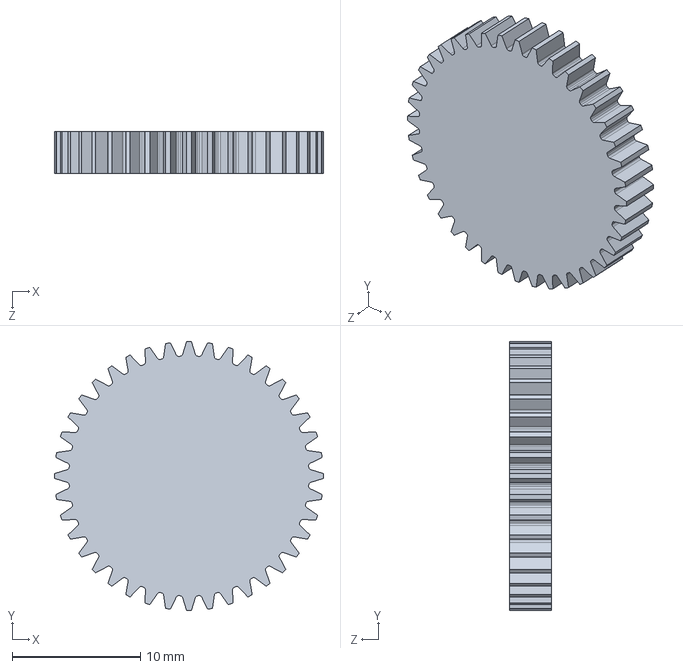
[picture p81: CAD file, 2024-02-01]
Version 2.2 Final/Nouvelle pièce/tunable-gear.SLDPRT
21.0 x 21.0 x 3.30 mm
